minou65/DCC_zDecoder/src/pinmapping.h

// pinmapping.h

#ifndef _PINMAPPING_h
#define _PINMAPPING_h

#if defined(ARDUINO) && ARDUINO >= 100
	#include "arduino.h"
#else
	#include "WProgram.h"
#endif

// https://randomnerdtutorials.com/esp32-pinout-reference-gpios/
// Recommend only the following pins 2,4,12-19,21-23,25-27,32-33
// Ensure no pin assignments in your Sketch or Libraries are using 
// the IO19 or IO20 to ensure the USB Debugging works correctly.

// All boards support the vMicro Software Debugger which only requires 
// the Serial interface to work

static uint8_t OutputIndexToPin[16] PROGMEM = {
	GPIO_NUM_23, // O11
	GPIO_NUM_22, // O12
	GPIO_NUM_21, // O13
	GPIO_NUM_19, // O14
	GPIO_NUM_18, // O15
	GPIO_NUM_17, // O16
	GPIO_NUM_16, // O17
	GPIO_NUM_4,  // O18

	GPIO_NUM_33, // O21
	GPIO_NUM_32, // O22
	GPIO_NUM_25, // O23
	GPIO_NUM_26, // O24
	GPIO_NUM_27, // O25
	GPIO_NUM_14, // O26
	GPIO_NUM_12, // O27
	GPIO_NUM_13  // O28

};

const size_t MAX_OUTPUT_PINS = sizeof(OutputIndexToPin) / sizeof(OutputIndexToPin[0]);
const size_t MAX_INPUT_PINS = 0; // No input pins defined

enum class PinGroup {
	Output,
	Servo,
	Input
};

inline int getPinFromIndex(PinGroup group, size_t index) {
	switch (group) {
	case PinGroup::Output:
		if (index < MAX_OUTPUT_PINS) return OutputIndexToPin[index];
		break;
	case PinGroup::Servo:
		//if (index < MAX_SERVO_PINS) return ServoIndexToPin[index];
		break;
	case PinGroup::Input:
		//if (index < MAX_INPUT_PINS) return InputIndexToPin[index];
		break;
	}
	return -1; // Ungültiger Index oder Gruppe
}

#endif
